cbm-instructions/bits-please/Bilder/Bohrschablone.jpg

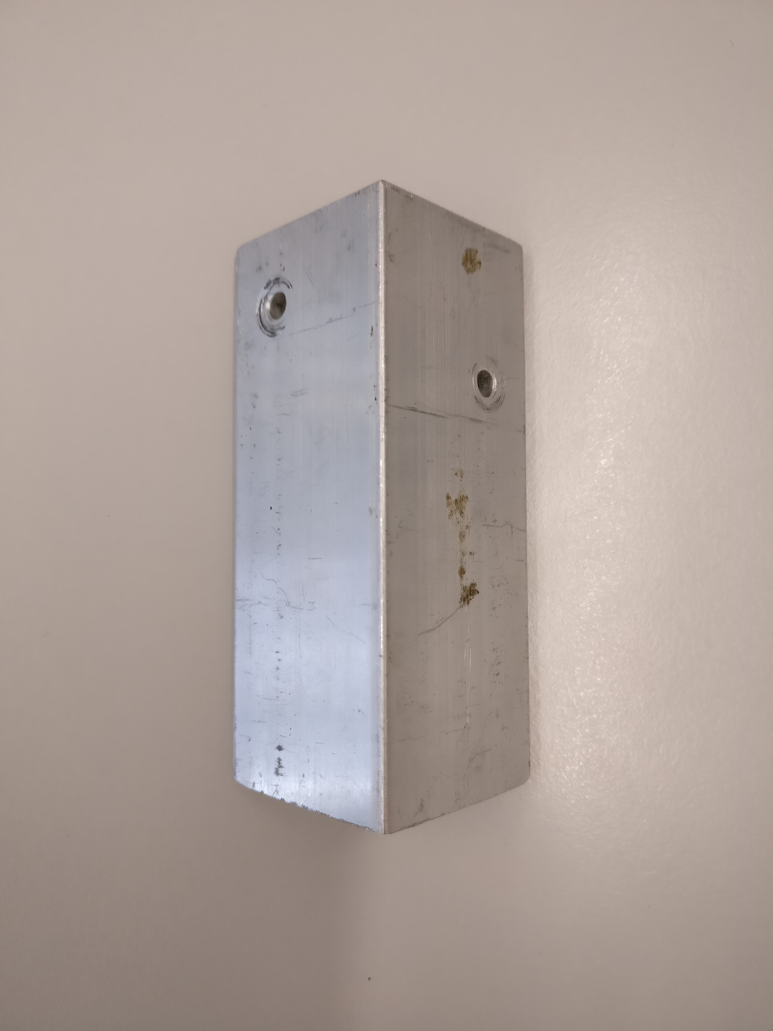
Bilder/Bohrschablone.jpg
