cbm-instructions/bits-please/Bilder/IMG_20170519_204449.jpg

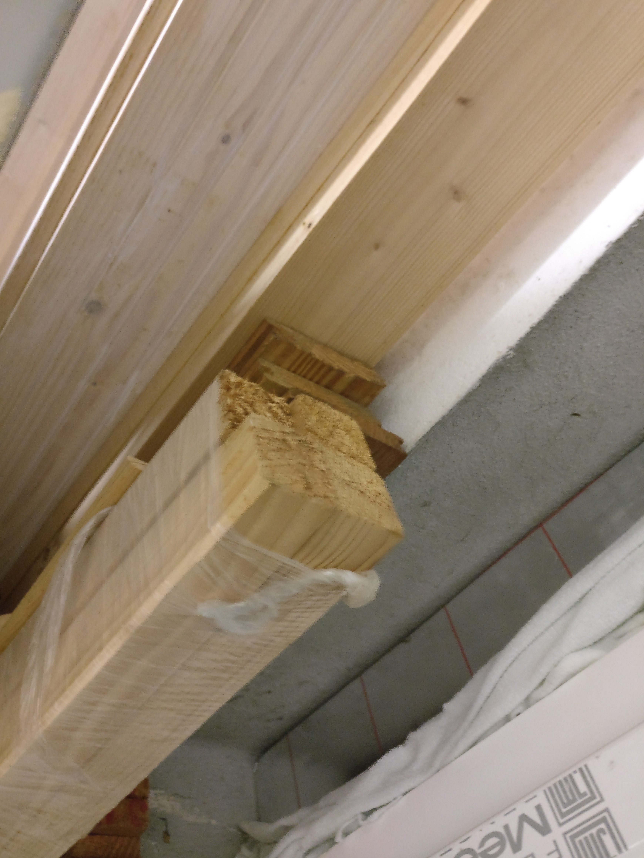
Bilder/IMG_20170519_204449.jpg
