cbm-instructions/bits-please/Bilder/IMG_20170519_205301.jpg

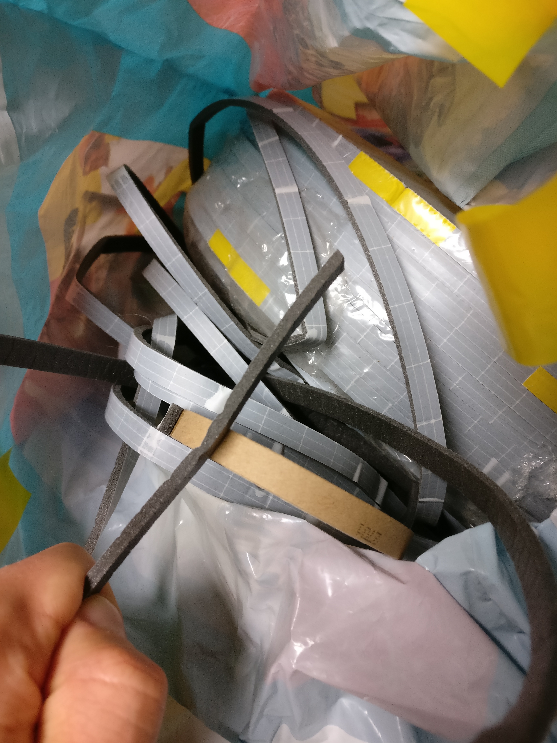
Bilder/IMG_20170519_205301.jpg
