cbm-instructions/bits-please/Bilder/IMG_20170519_211010.jpg

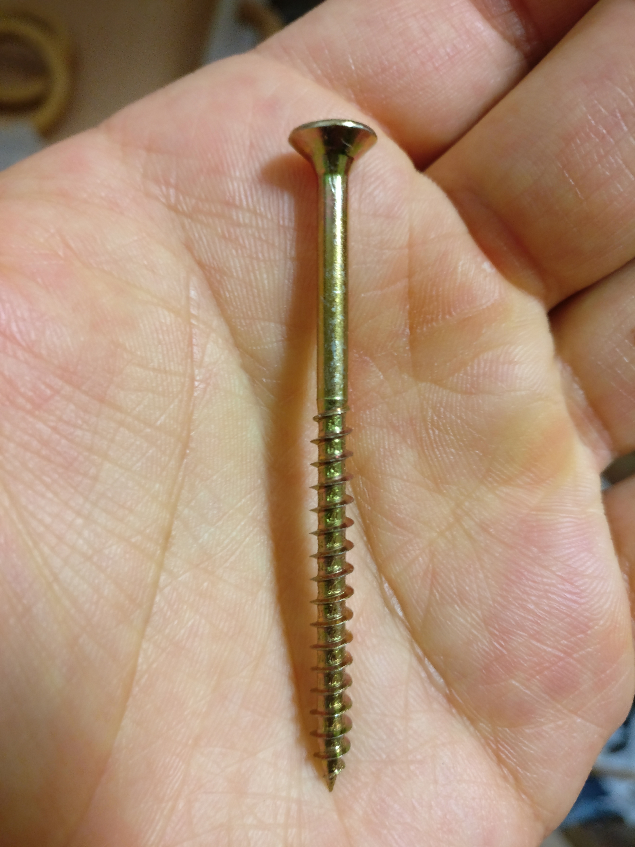
Bilder/IMG_20170519_211010.jpg
