cbm-instructions/bits-please/Bilder/IMG_20170519_211933.jpg

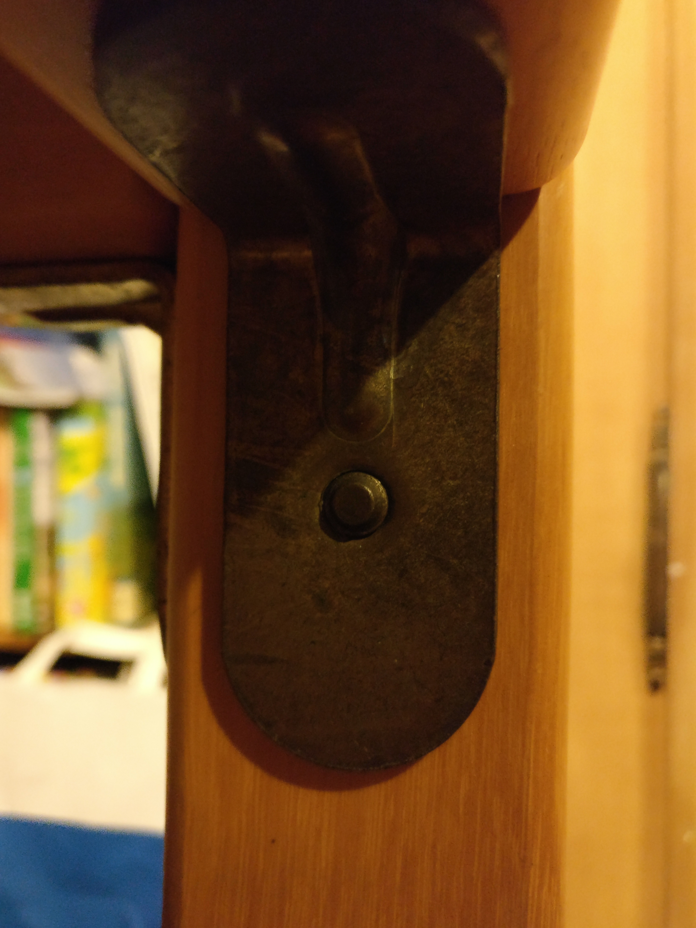
Bilder/IMG_20170519_211933.jpg
