cbm-instructions/bits-please/Bilder/IMG_20170520_222246.jpg

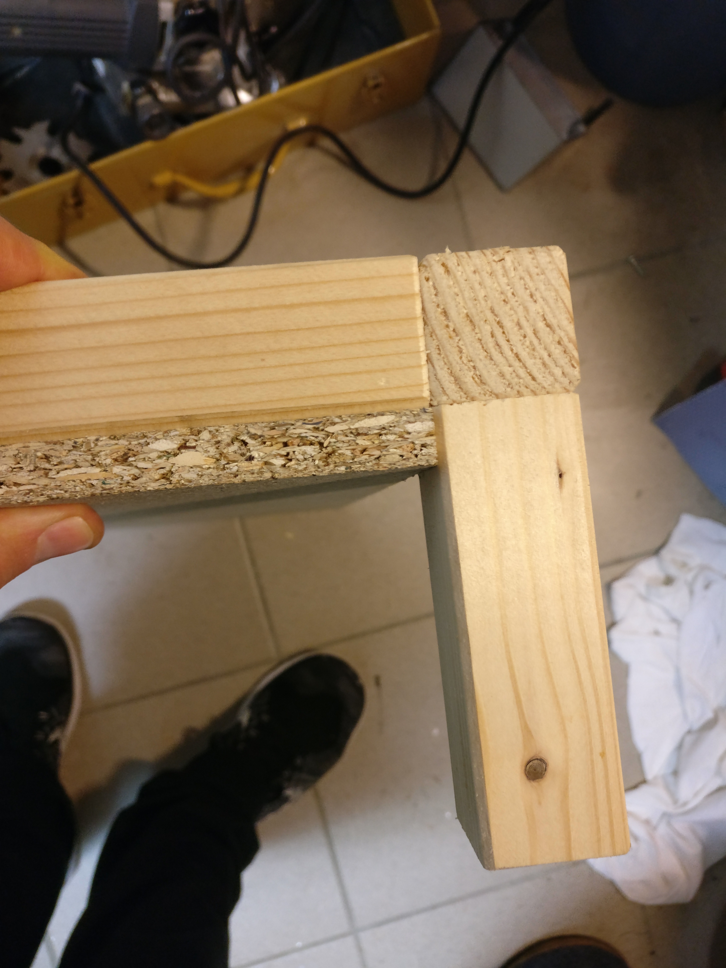
Bilder/IMG_20170520_222246.jpg
