cbm-instructions/bits-please/Bilder/IMG_20170520_222431.jpg

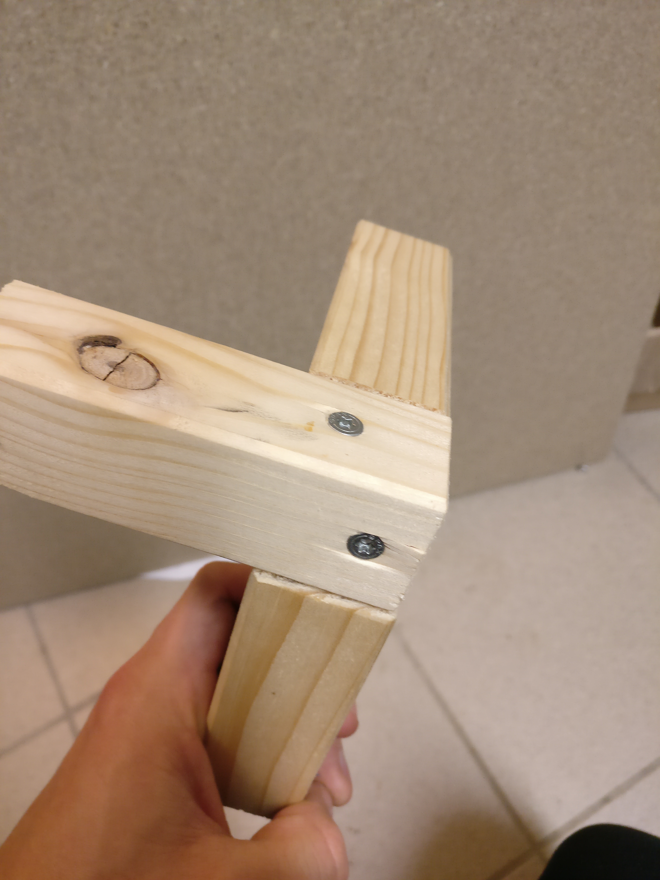
Bilder/IMG_20170520_222431.jpg
