cbm-instructions/bits-please/Bilder/IMG_20170527_123232.jpg

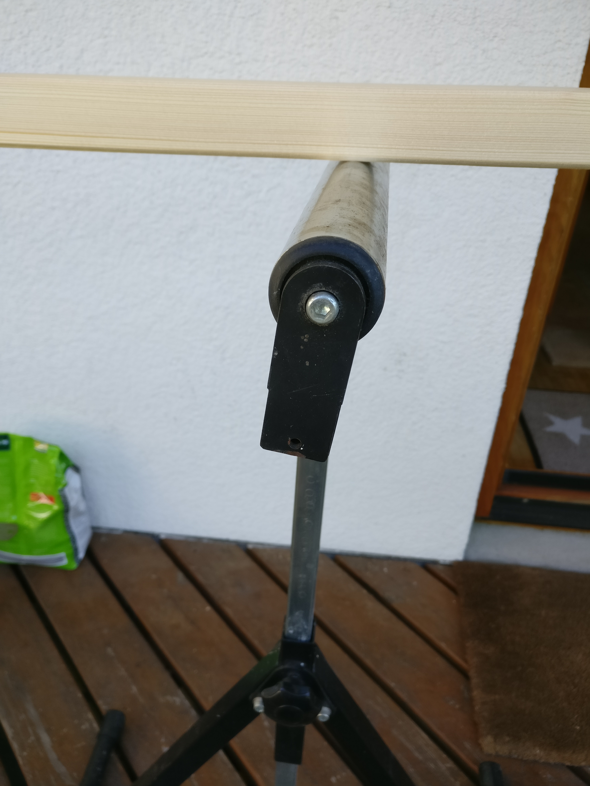
Bilder/IMG_20170527_123232.jpg
