cbm-instructions/bits-please/Bilder/IMG_20170527_123247.jpg

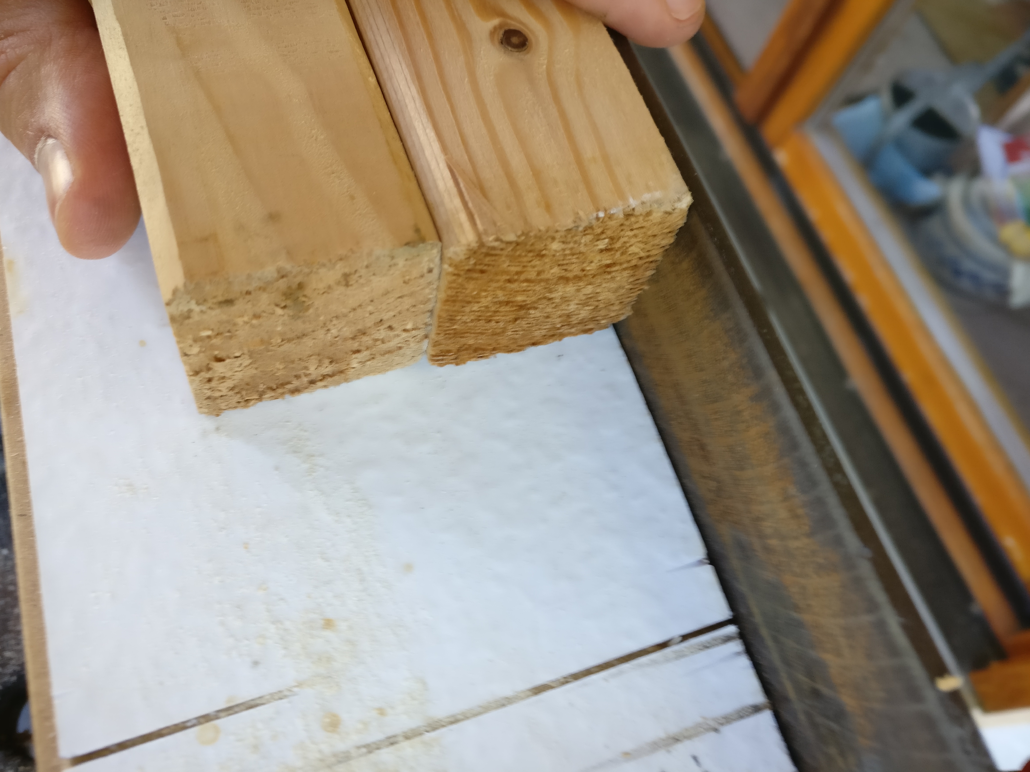
Bilder/IMG_20170527_123247.jpg
