cbm-instructions/bits-please/Bilder/IMG_20170527_123250.jpg

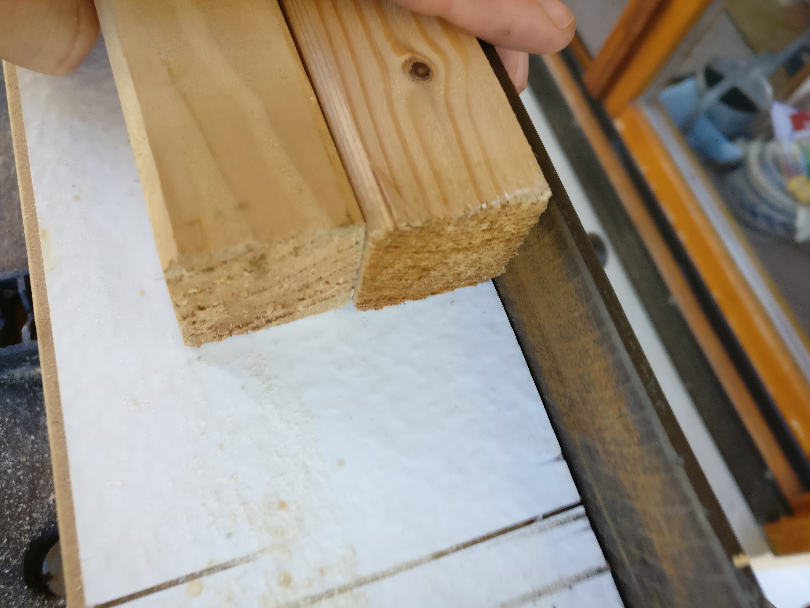
Bilder/IMG_20170527_123250.jpg
