cbm-instructions/bits-please/Bilder/IMG_20170527_123333.jpg

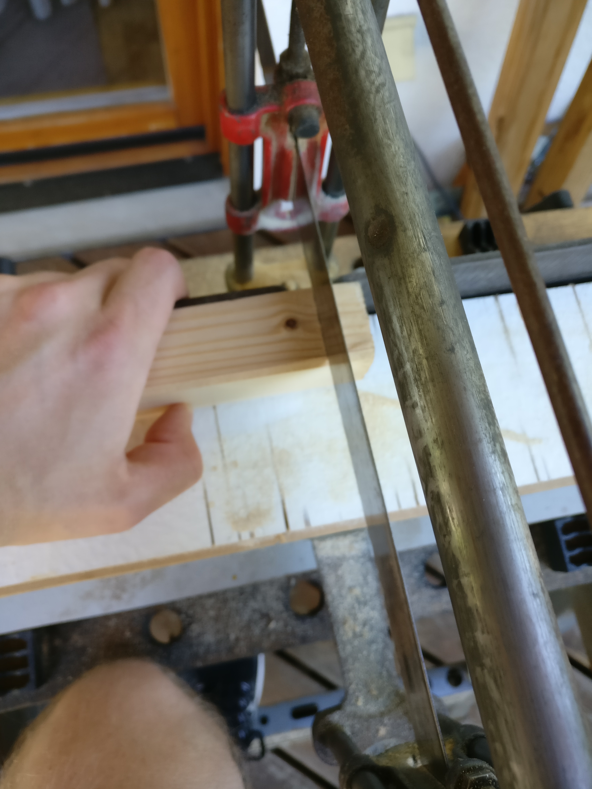
Bilder/IMG_20170527_123333.jpg
