cbm-instructions/bits-please/Bilder/IMG_20170527_165500.jpg

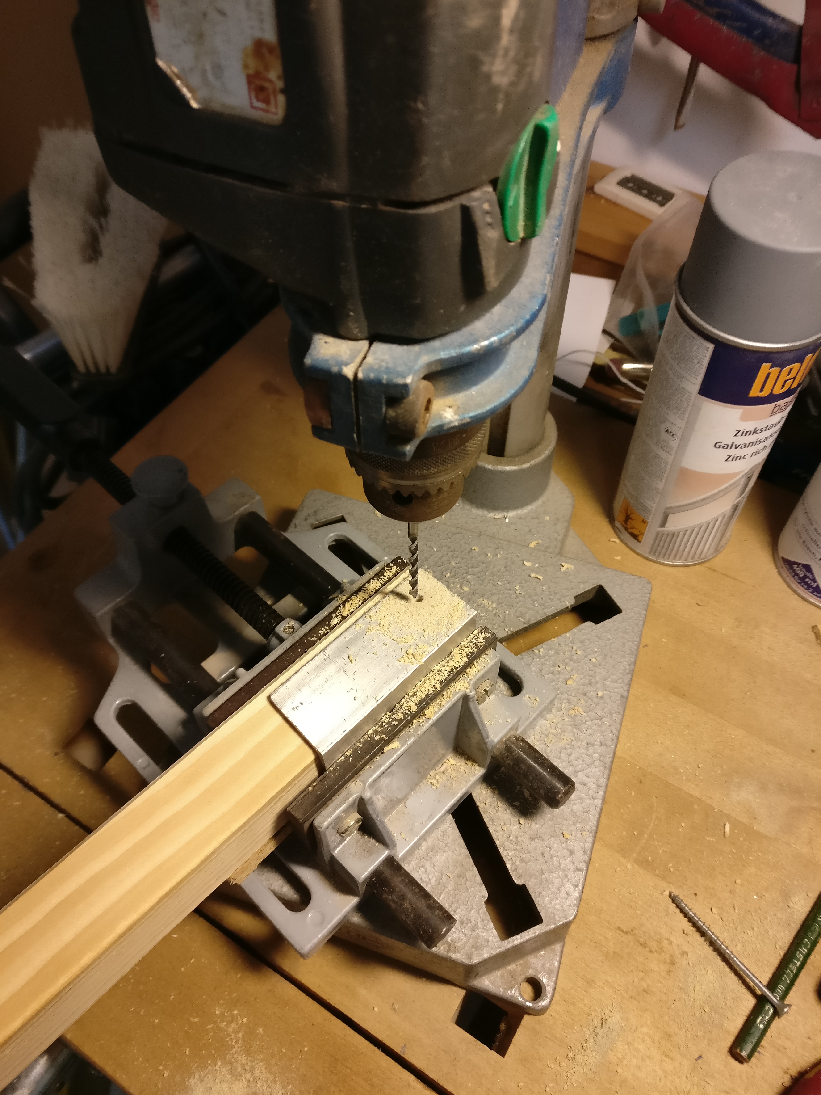
Bilder/IMG_20170527_165500.jpg
