cbm-instructions/bits-please/Bilder/IMG_20170609_144201.jpg

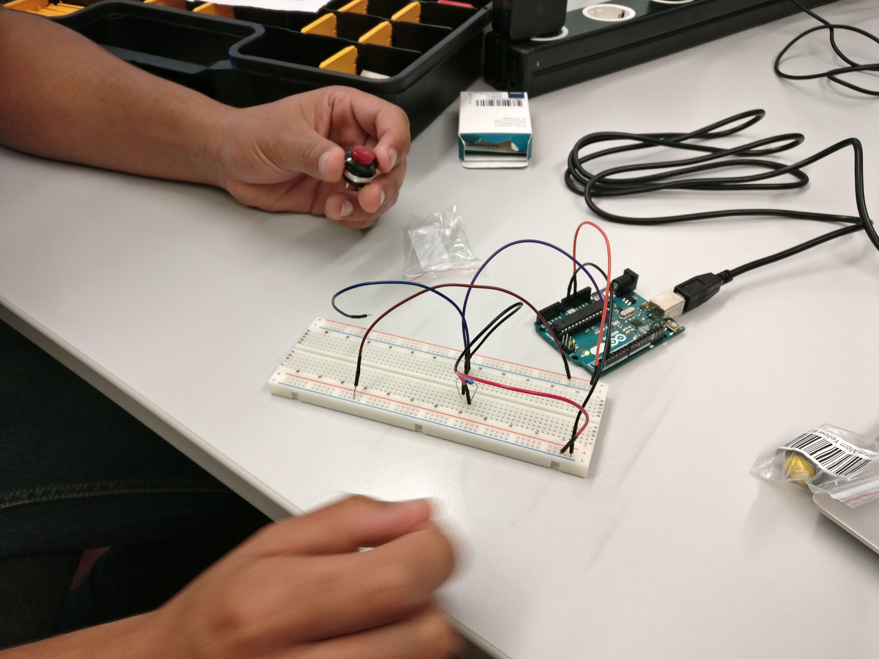
Bilder/IMG_20170609_144201.jpg
