cbm-instructions/bits-please/Bilder/IMG_20170612_164135.jpg

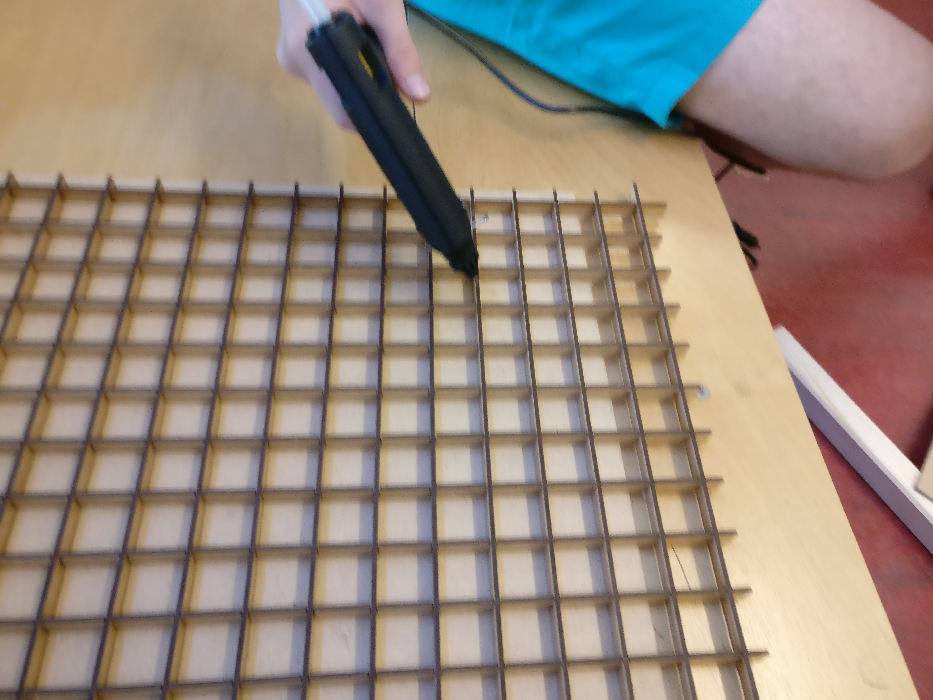
Bilder/IMG_20170612_164135.jpg
