cbm-instructions/bits-please/Bilder/IMG_20170612_164253.jpg

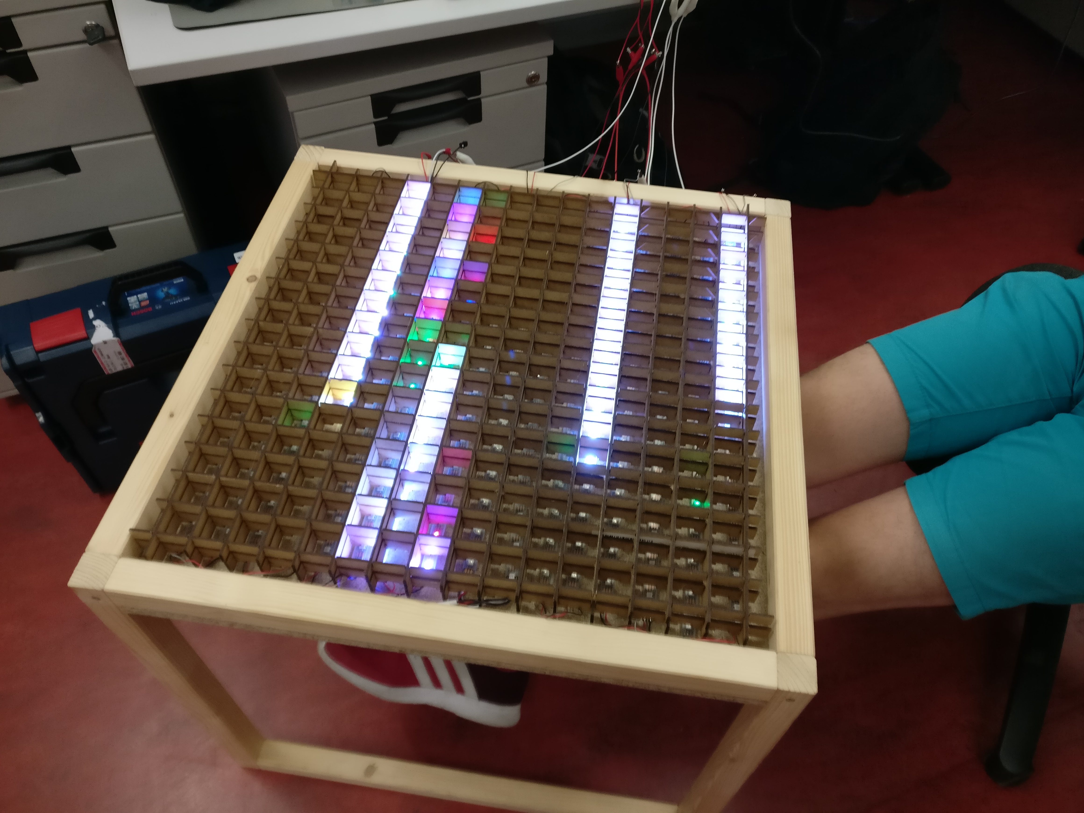
Bilder/IMG_20170612_164253.jpg
