cbm-instructions/bits-please/Bilder/IMG_20170612_170641.jpg

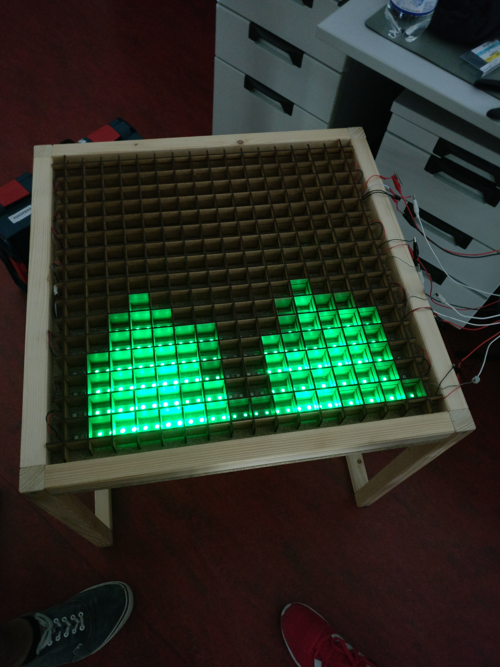
Bilder/IMG_20170612_170641.jpg
