cbm-instructions/bits-please/Bilder/IMG_20170612_170821.jpg

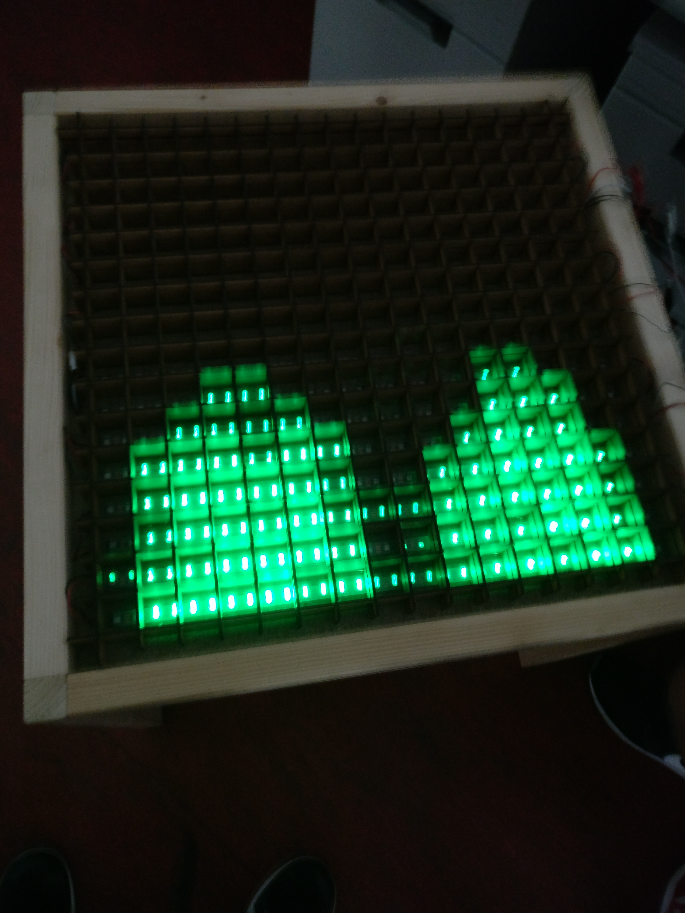
Bilder/IMG_20170612_170821.jpg
