cbm-instructions/bits-please/Bilder/IMG_20170612_174148.jpg

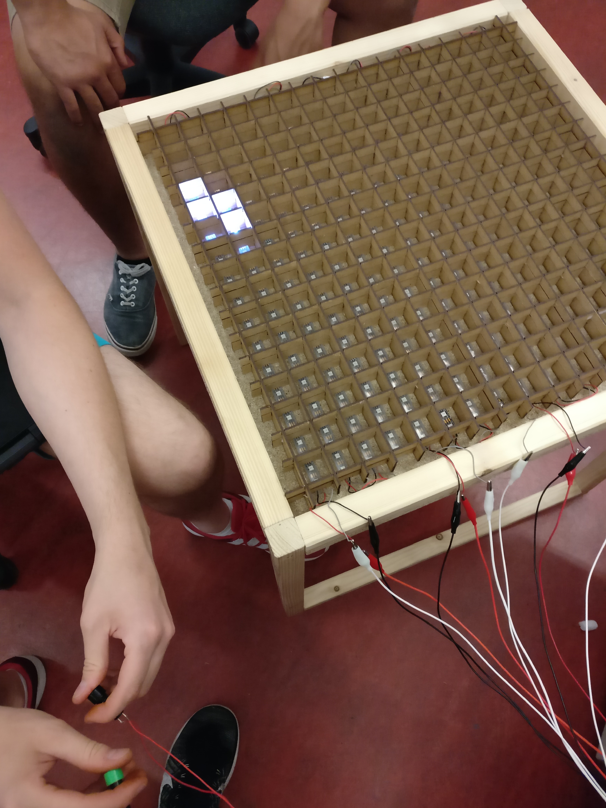
Bilder/IMG_20170612_174148.jpg
