cbm-instructions/bits-please/Bilder/IMG_20170612_175354.jpg

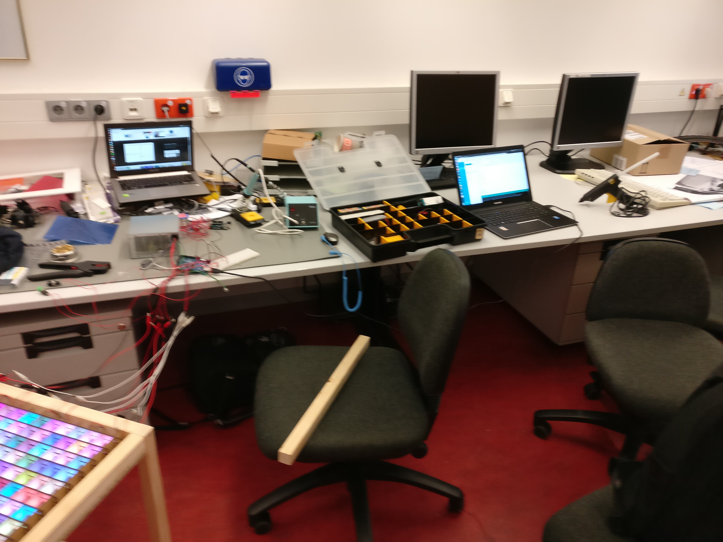
Bilder/IMG_20170612_175354.jpg
