cbm-instructions/bits-please/Bilder/IMG_20170612_180323.jpg

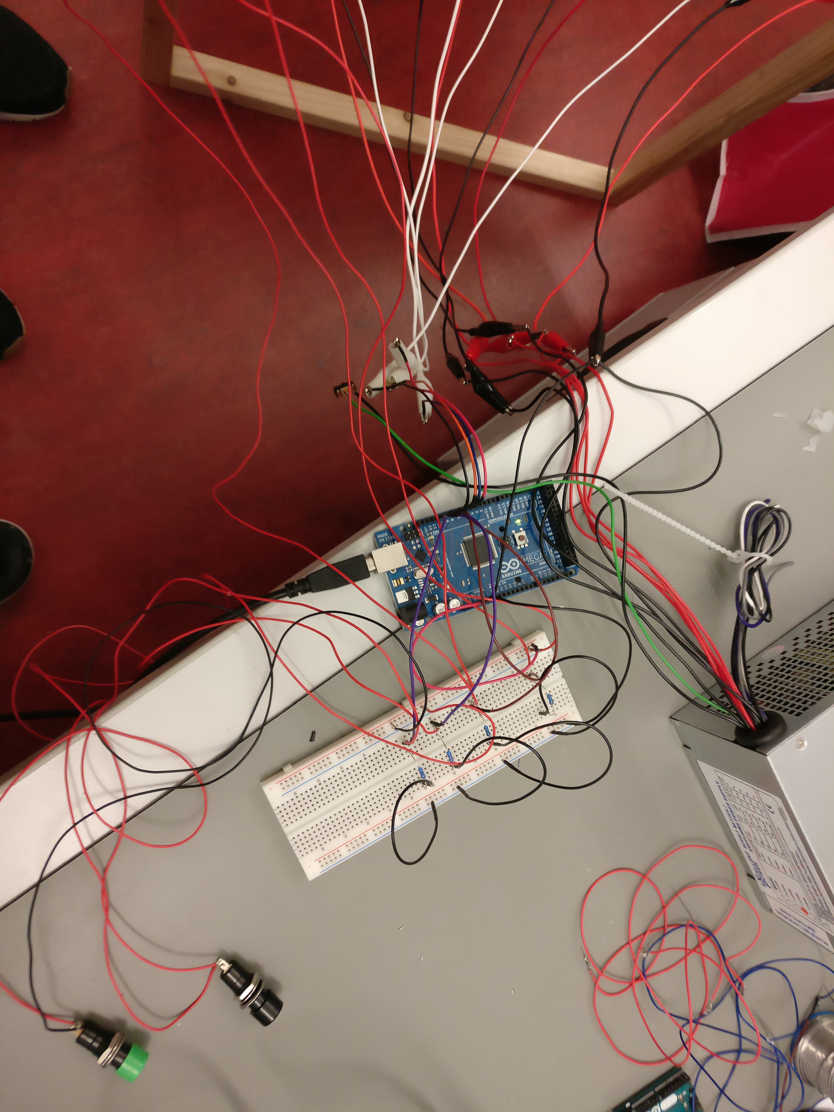
Bilder/IMG_20170612_180323.jpg
