cbm-instructions/bits-please/Bilder/IMG_20170612_180538.jpg

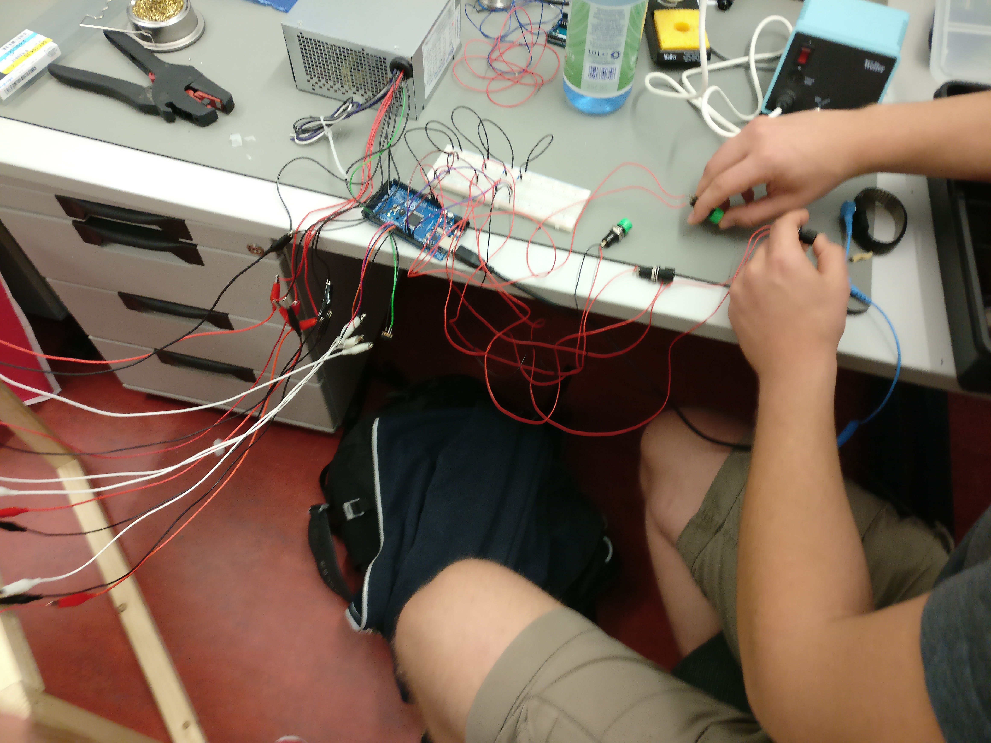
Bilder/IMG_20170612_180538.jpg
