cbm-instructions/bits-please/Bilder/IMG_20170612_180732.jpg

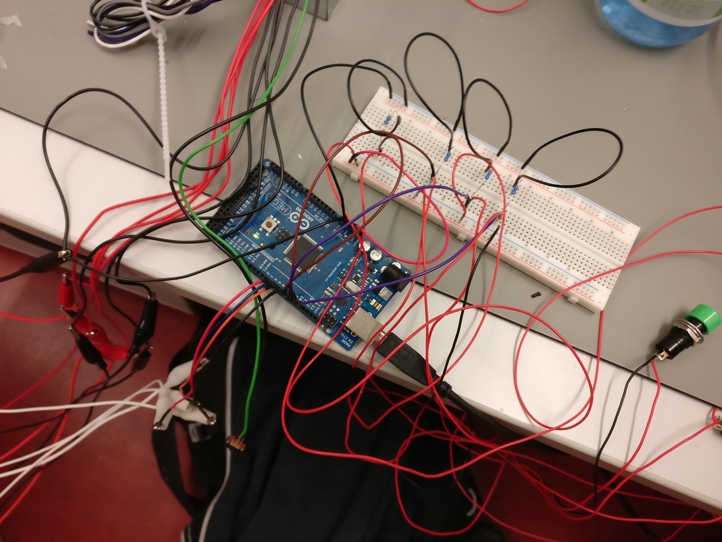
Bilder/IMG_20170612_180732.jpg
