cbm-instructions/bits-please/Bilder/IMG_20170613_182310.jpg

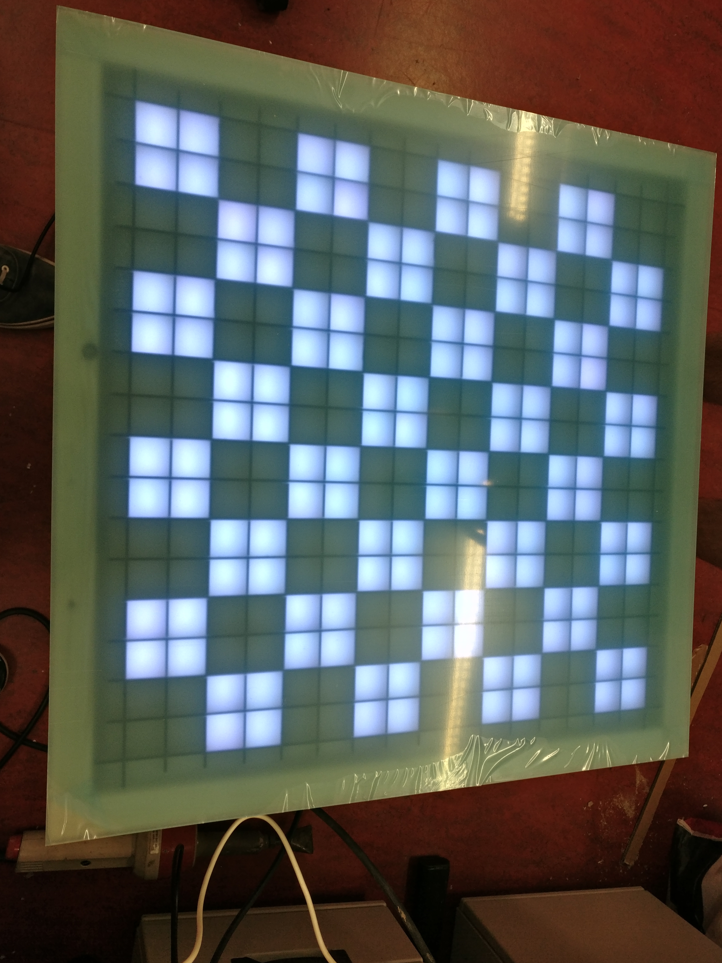
Bilder/IMG_20170613_182310.jpg
