cbm-instructions/bits-please/Bilder/IMG_20170614_124438.jpg

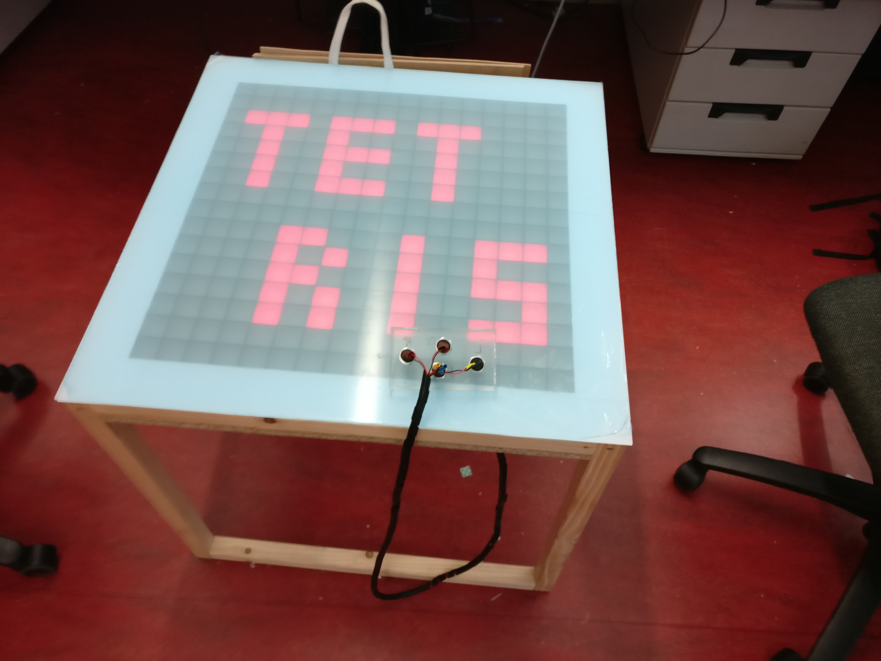
Bilder/IMG_20170614_124438.jpg
