cbm-instructions/bits-please/Bilder/IMG_20170617_104437.jpg

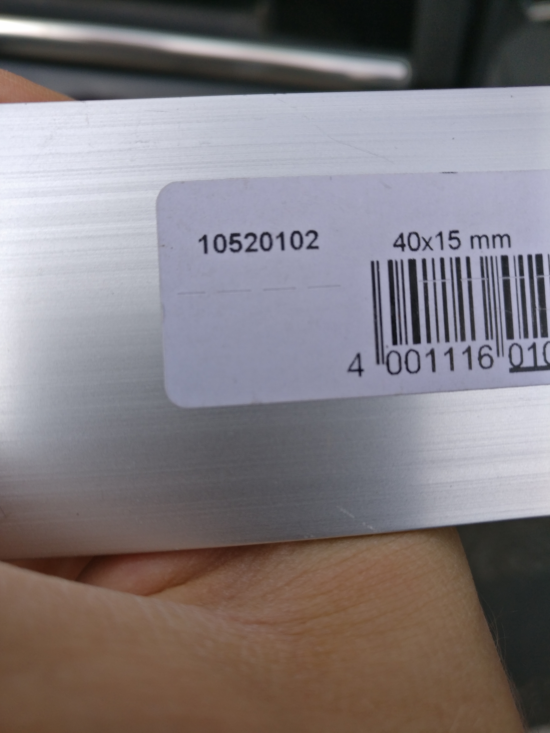
Bilder/IMG_20170617_104437.jpg
