cbm-instructions/bits-please/Bilder/IMG_20170617_104439.jpg

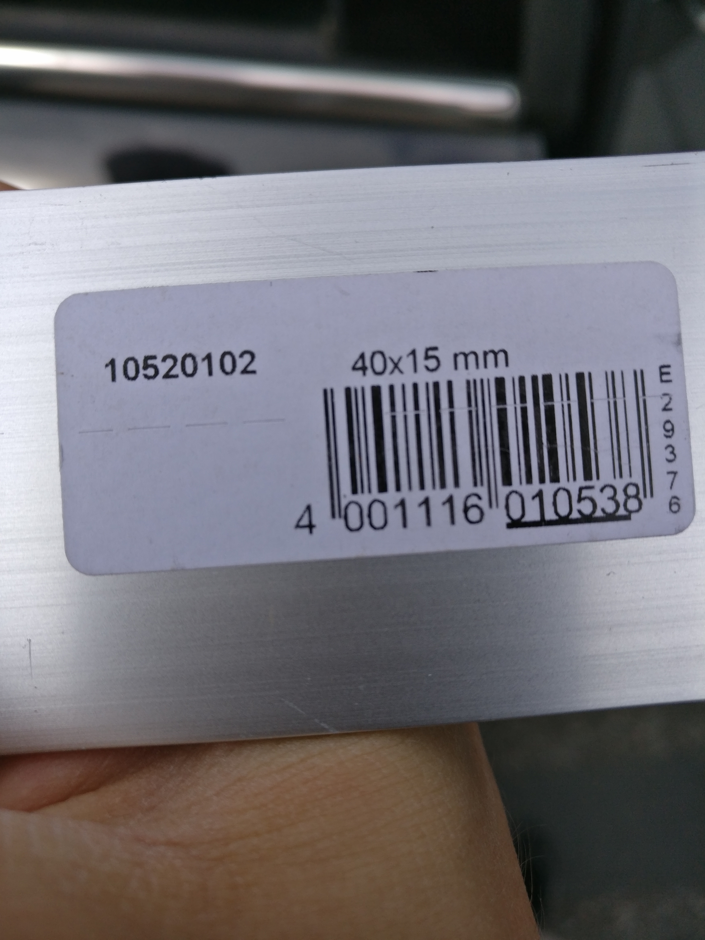
Bilder/IMG_20170617_104439.jpg
