cbm-instructions/bits-please/Bilder/IMG_20170617_122034.jpg

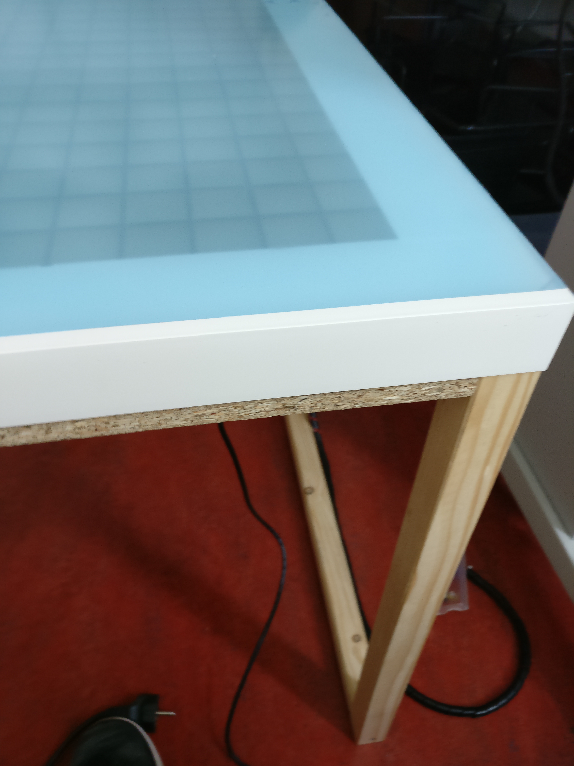
Bilder/IMG_20170617_122034.jpg
