cbm-instructions/bits-please/Bilder/IMG_20170617_122047.jpg

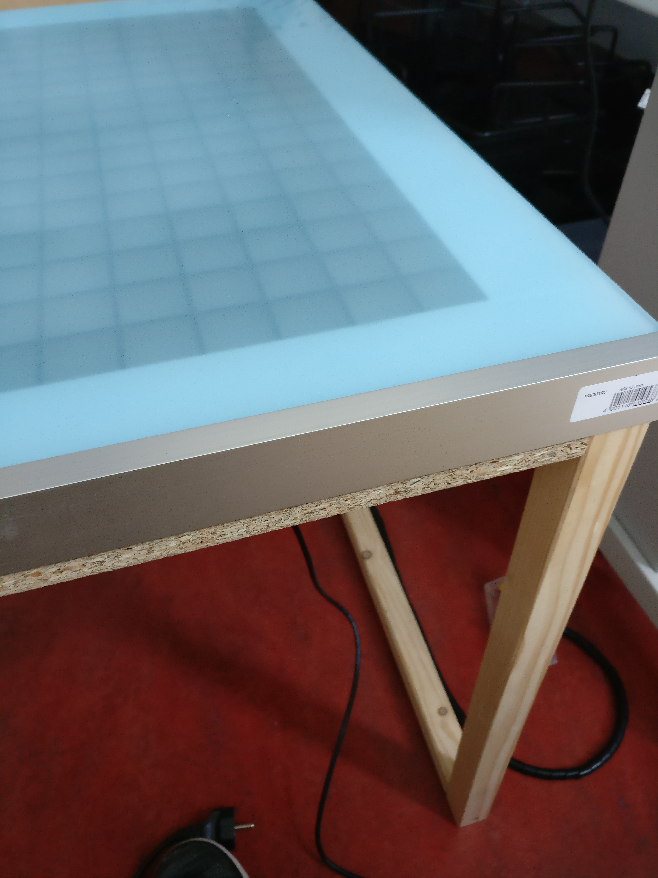
Bilder/IMG_20170617_122047.jpg
