cbm-instructions/bits-please/Bilder/IMG_20170617_122103.jpg

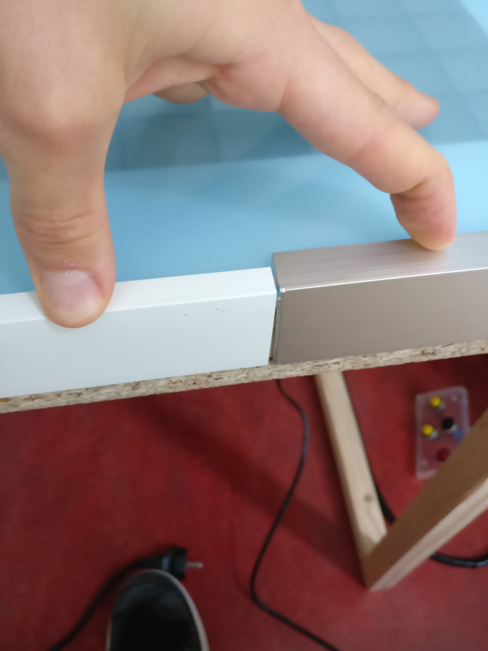
Bilder/IMG_20170617_122103.jpg
