cbm-instructions/bits-please/Bilder/IMG_20170617_122408.jpg

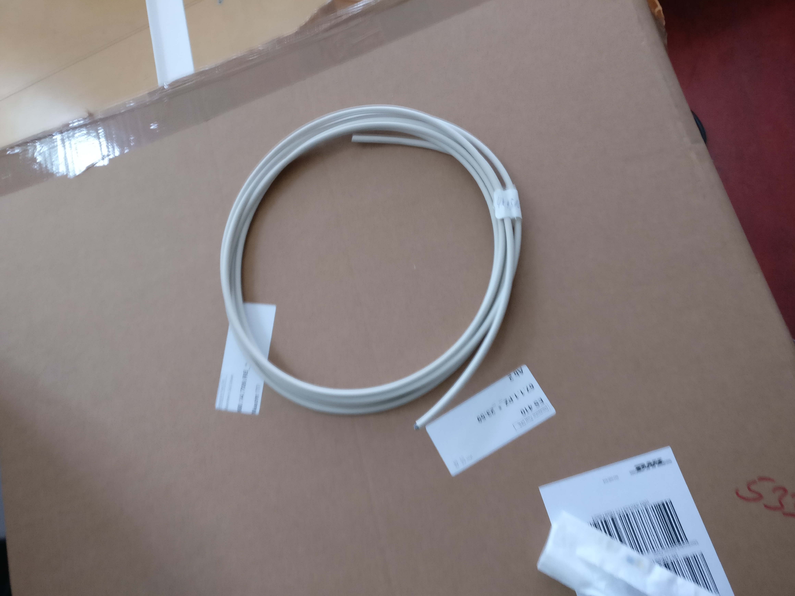
Bilder/IMG_20170617_122408.jpg
