cbm-instructions/bits-please/Bilder/IMG_20170622_221234.jpg

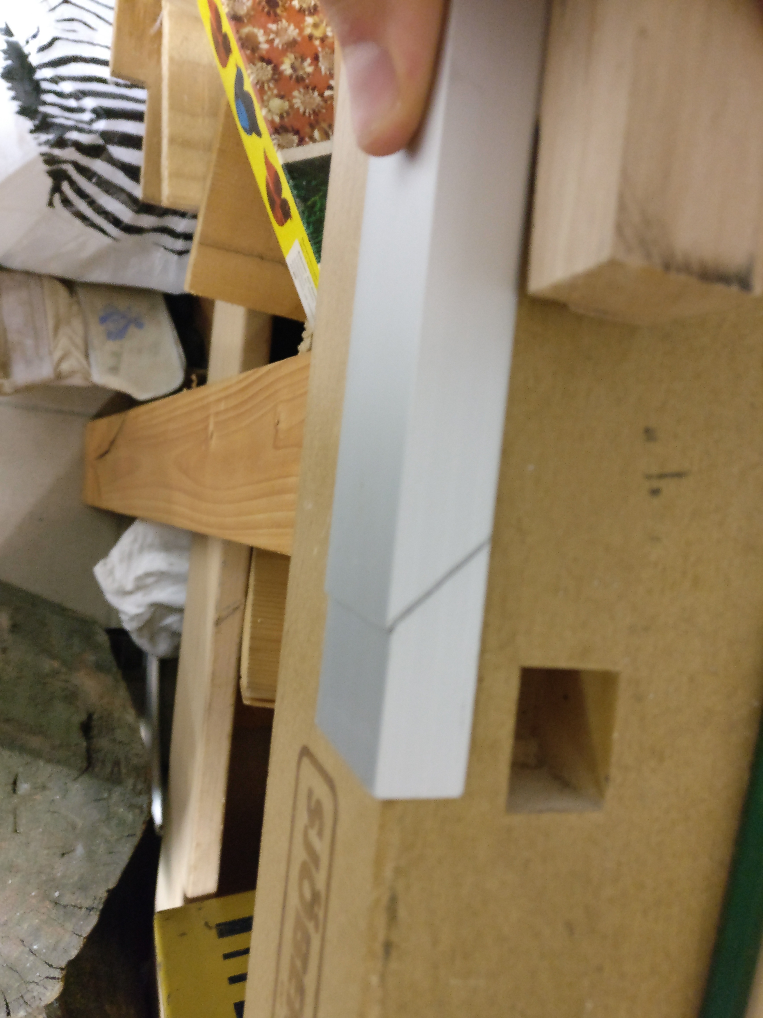
Bilder/IMG_20170622_221234.jpg
