cbm-instructions/bits-please/Bilder/IMG_20170622_221240.jpg

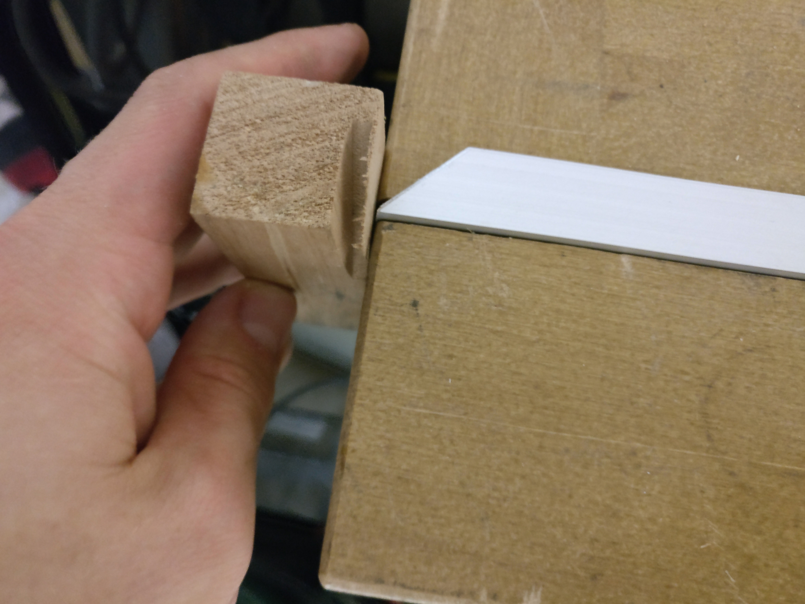
Bilder/IMG_20170622_221240.jpg
