cbm-instructions/bits-please/Bilder/IMG_20170622_221611.jpg

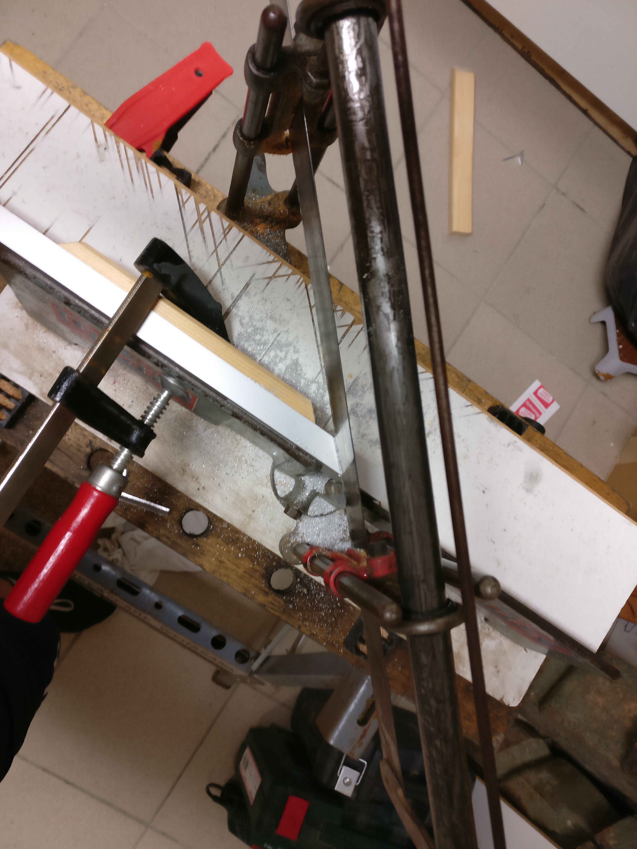
Bilder/IMG_20170622_221611.jpg
