cbm-instructions/bits-please/Bilder/IMG_20170622_221712.jpg

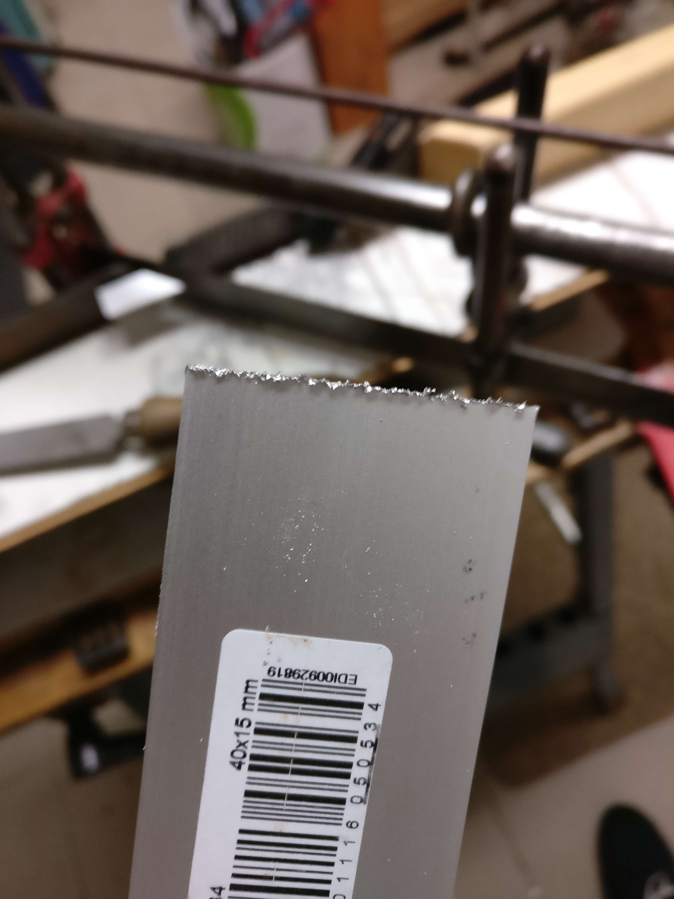
Bilder/IMG_20170622_221712.jpg
