cbm-instructions/bits-please/Bilder/IMG_20170622_231054.jpg

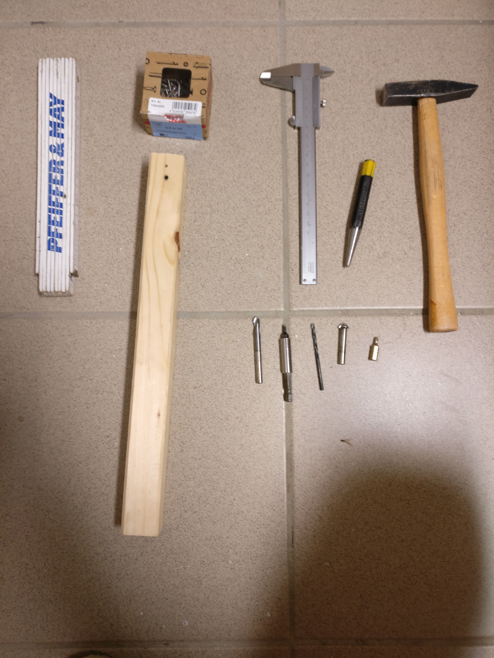
Bilder/IMG_20170622_231054.jpg
