cbm-instructions/bits-please/Bilder/IMG_20170622_231112.jpg

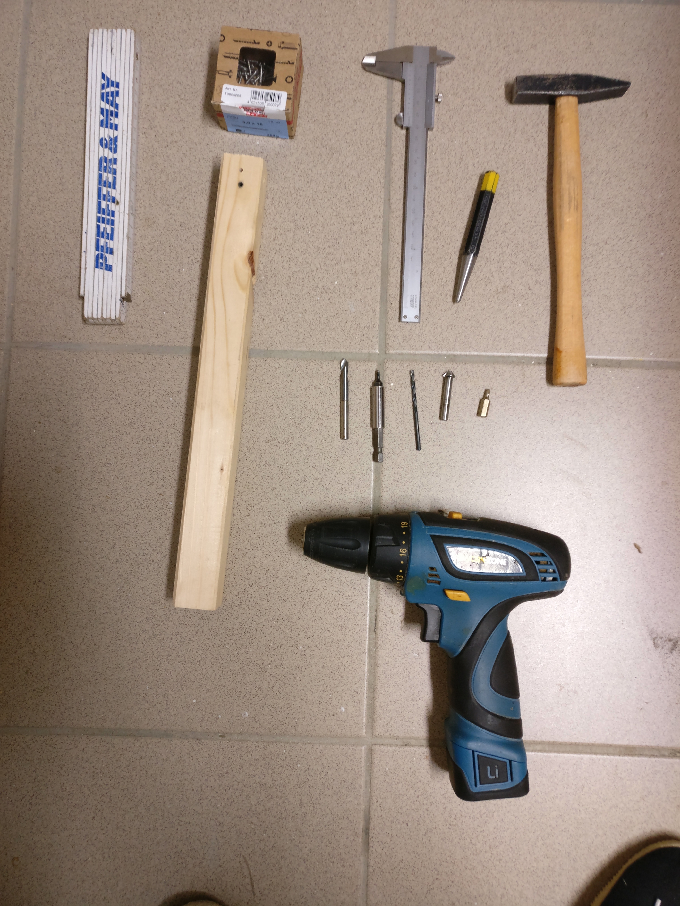
Bilder/IMG_20170622_231112.jpg
