cbm-instructions/bits-please/Controller/Magnete.jpg

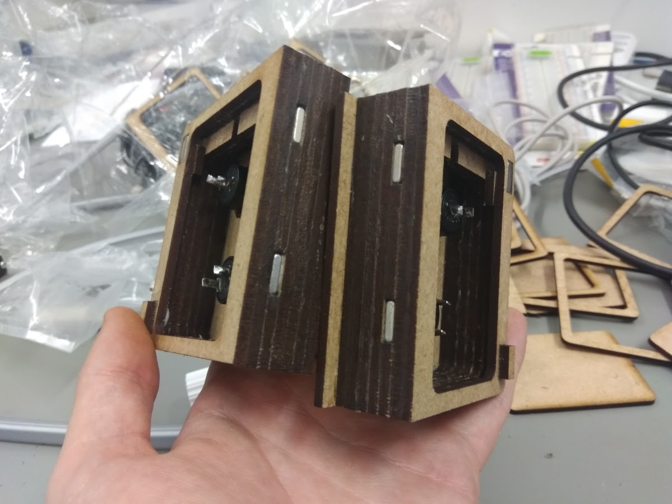
Controller/Magnete.jpg
