cbm-instructions/bits-please/Matrix/Diffusion.jpg

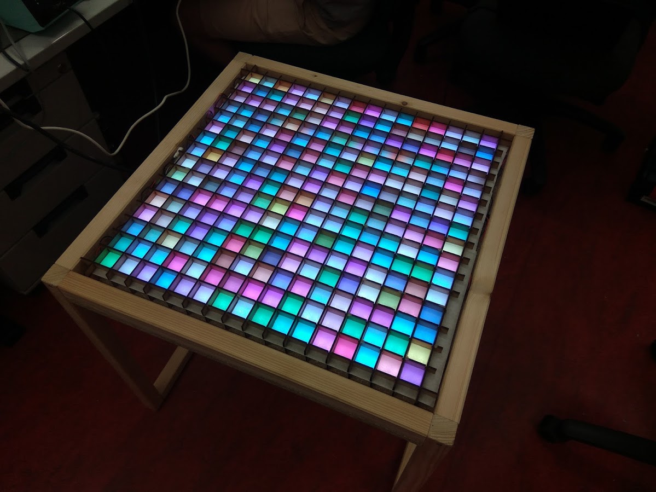
Matrix/Diffusion.jpg
